juanmcasillas/BLButtons/doc/1_esquema.png

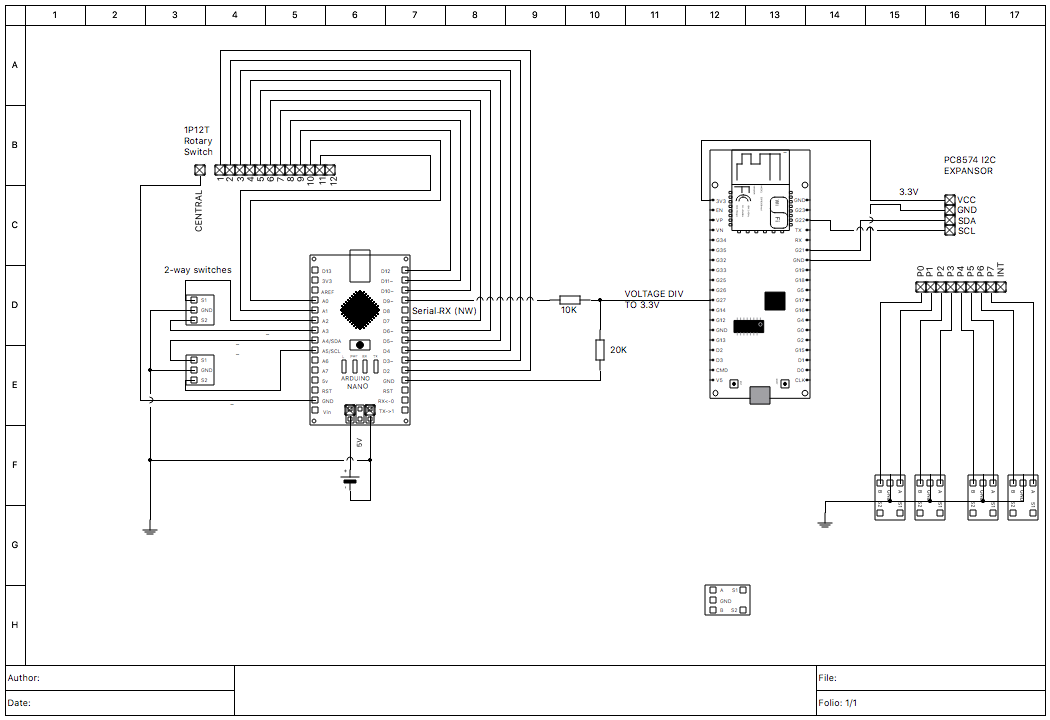
doc/1_esquema.png
