juanmcasillas/BLButtons/img/1p12t.jpg

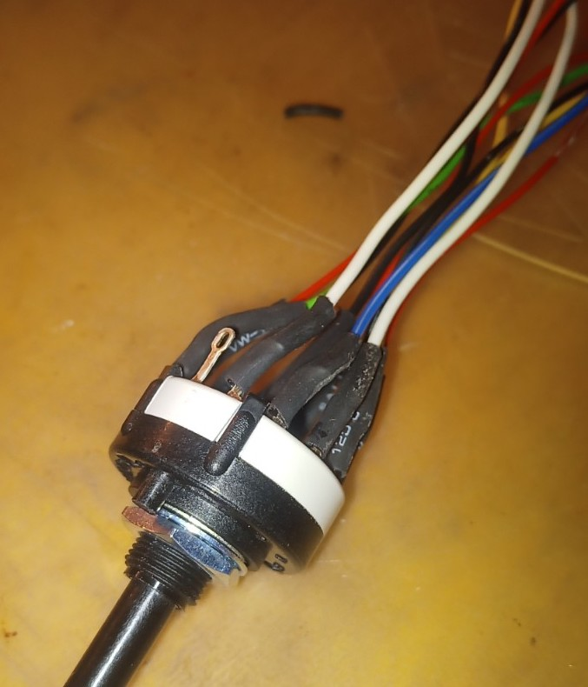
img/1p12t.jpg
