juanmcasillas/BLButtons/img/arduino_serial_esp32.jpg

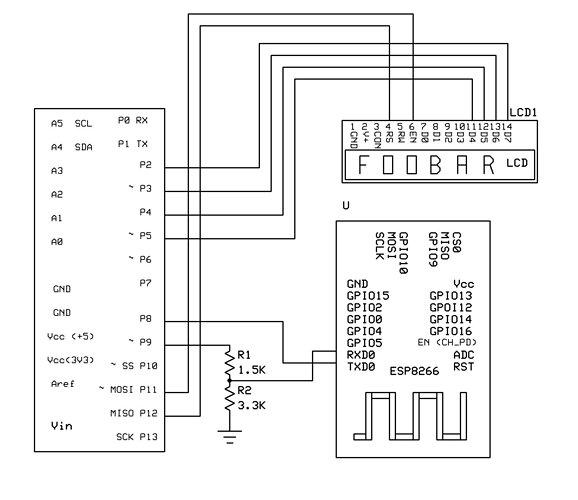
img/arduino_serial_esp32.jpg
