juanmcasillas/BLButtons/img/blbuttons.jpg

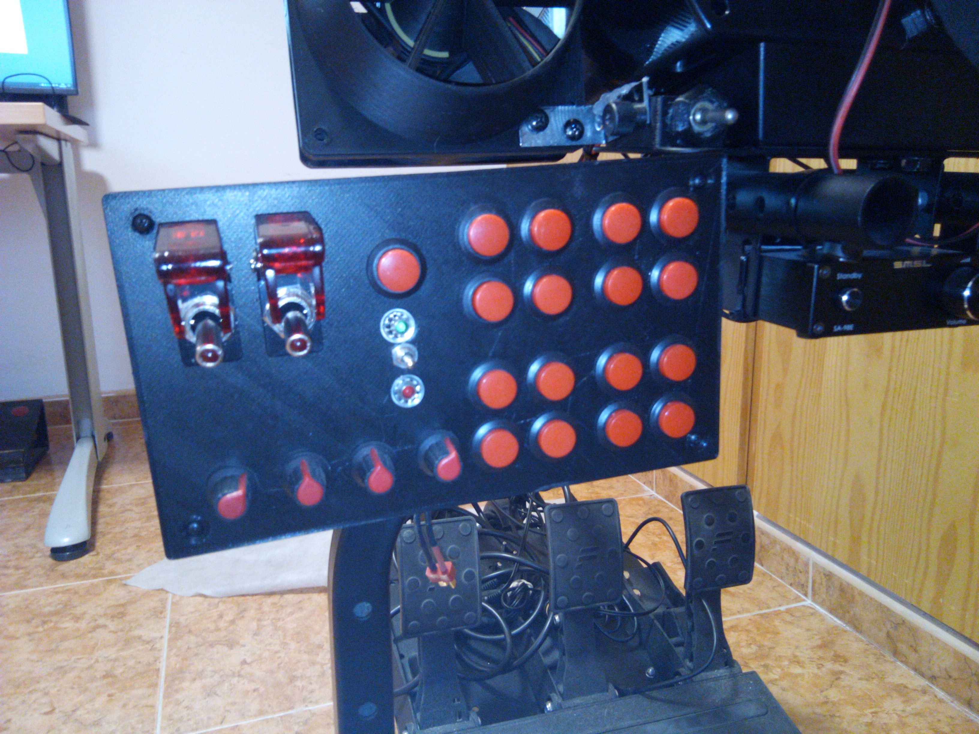
img/blbuttons.jpg
