juanmcasillas/BLButtons/img/box.jpg

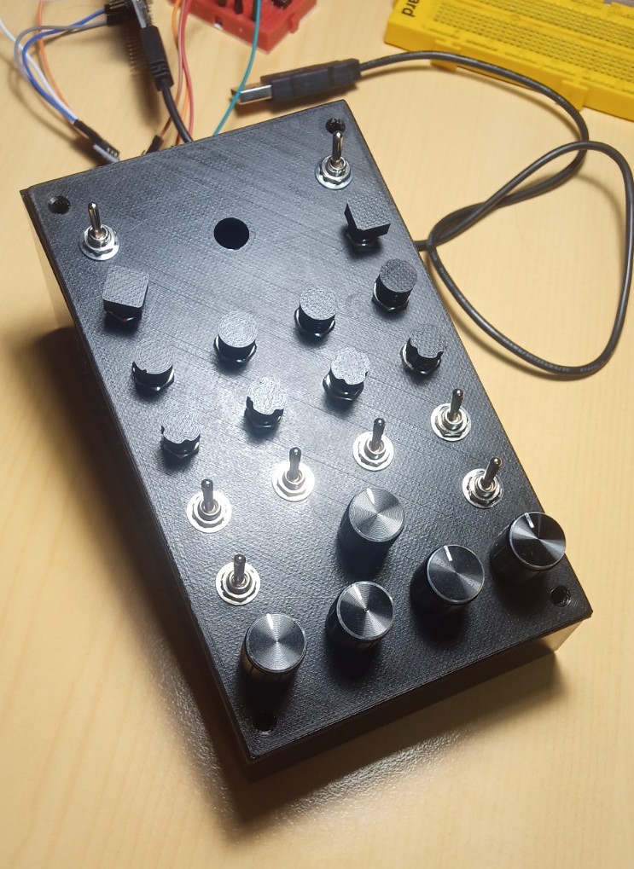
img/box.jpg
