juanmcasillas/BLButtons/img/esp32_photo.jpg

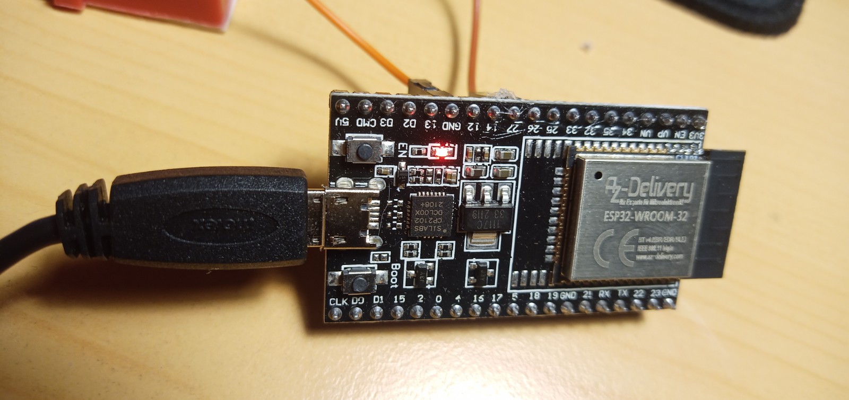
img/esp32_photo.jpg
