juanmcasillas/BLButtons/img/i2cexpansor.jpg

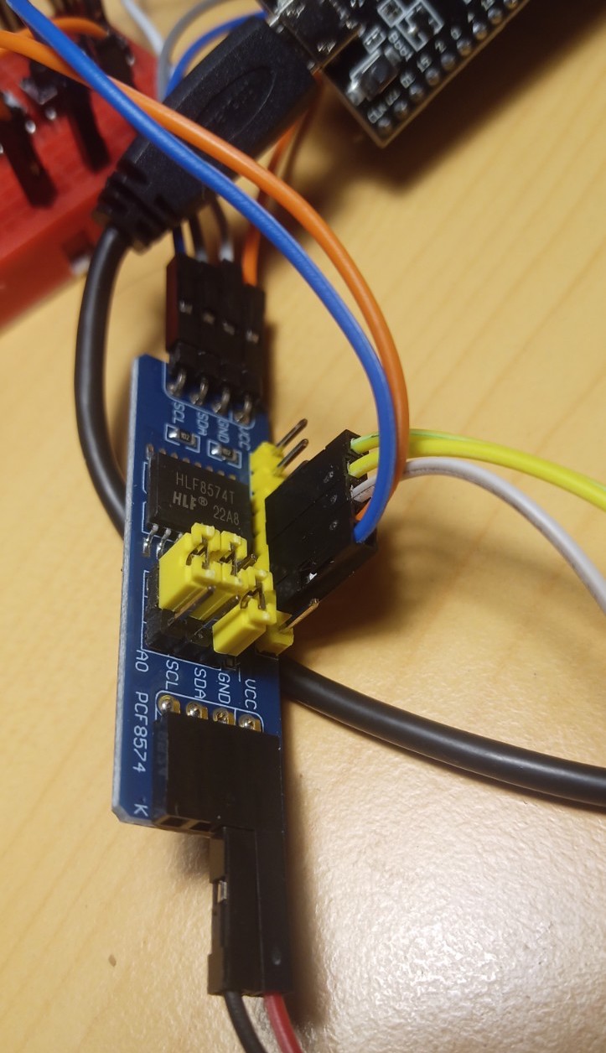
img/i2cexpansor.jpg
