juanmcasillas/BLButtons/img/keypad_matrix.png

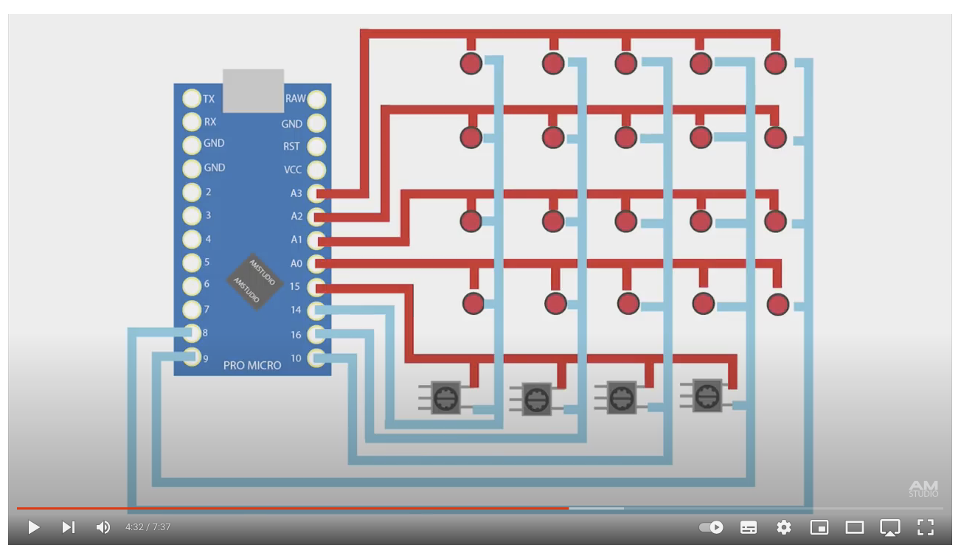
img/keypad_matrix.png
