juanmcasillas/BLButtons/img/keypad_matrix_encoder.png

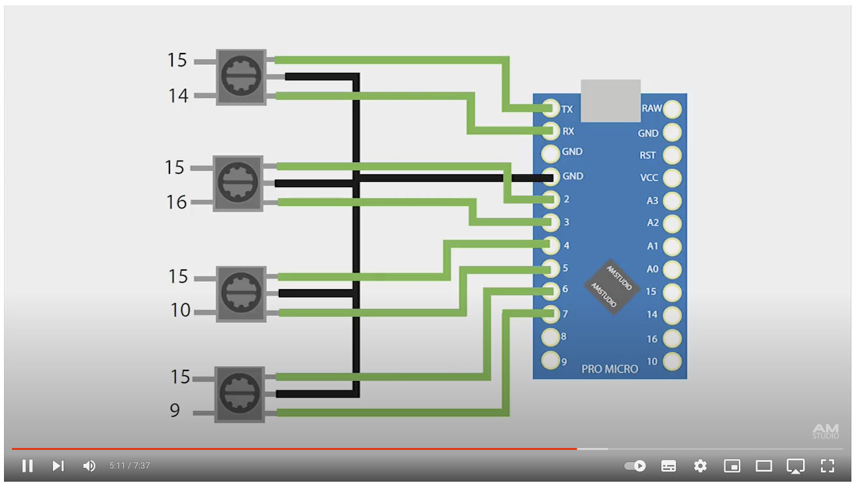
img/keypad_matrix_encoder.png
