juanmcasillas/BLButtons/img/keypadmatrix.png

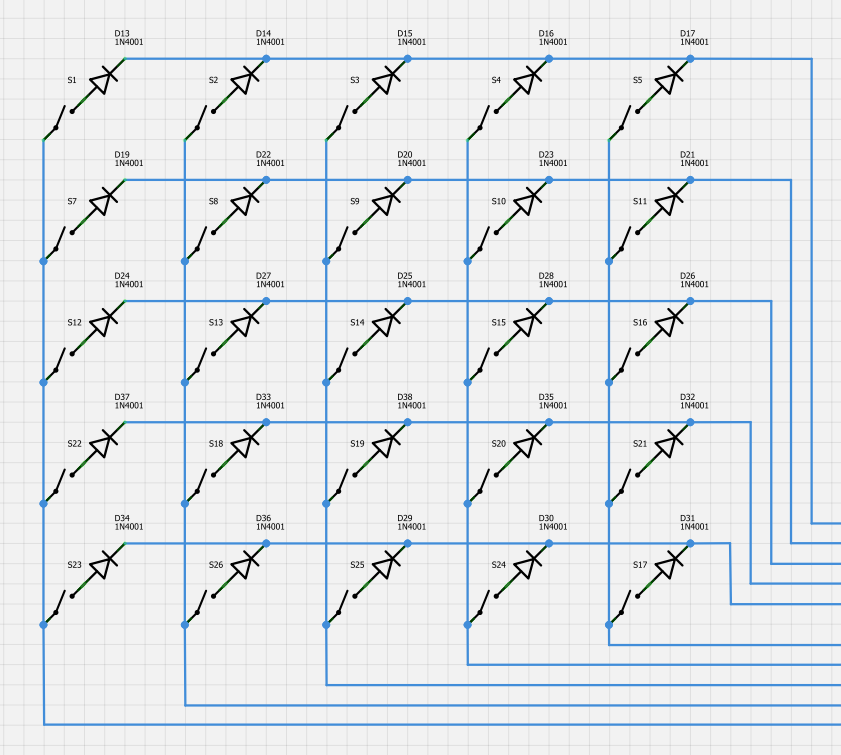
img/keypadmatrix.png
