juanmcasillas/BLButtons/img/ky_40.png

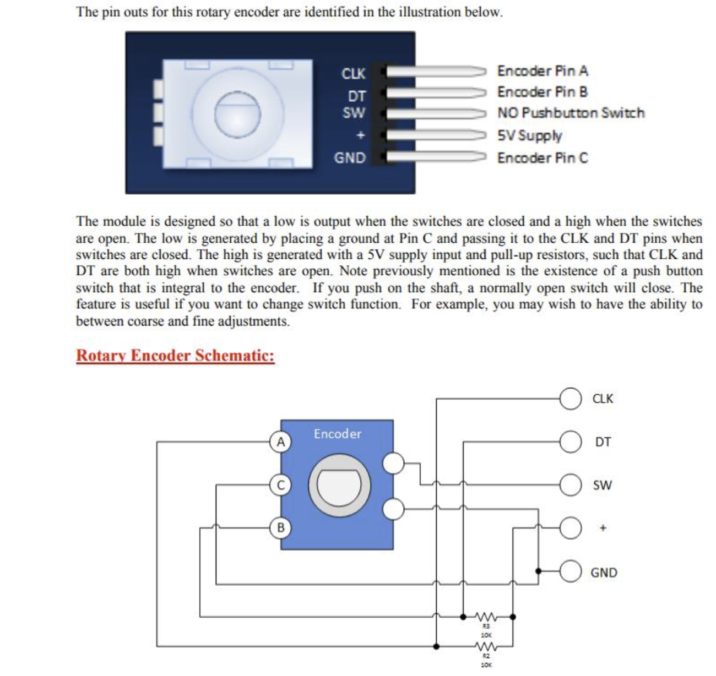
img/ky_40.png
