juanmcasillas/BLButtons/img/lever_cover_size.jpg

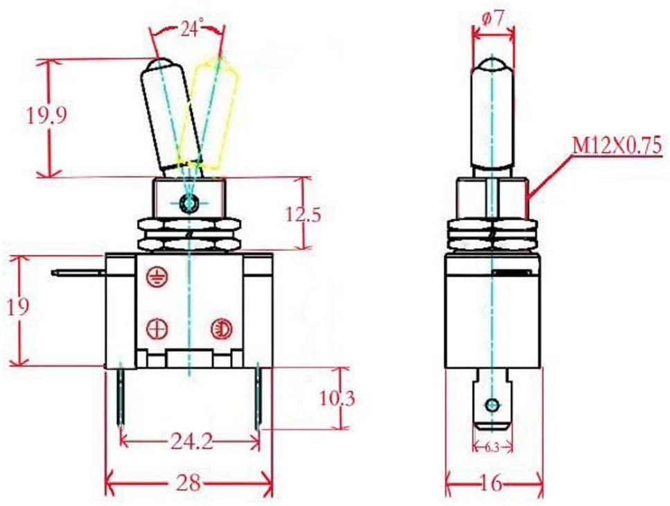
img/lever_cover_size.jpg
