juanmcasillas/BLButtons/img/lever_size.jpg

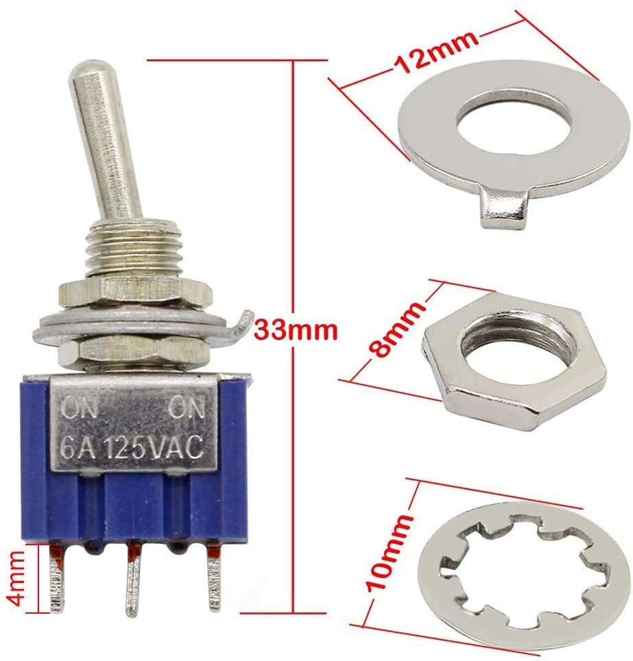
img/lever_size.jpg
