juanmcasillas/BLButtons/img/lever_size_cover.jpg

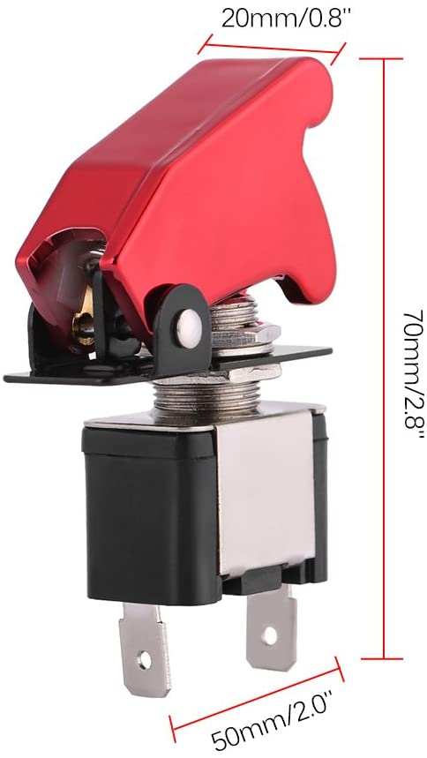
img/lever_size_cover.jpg
