juanmcasillas/BLButtons/img/PC8574module.jpg

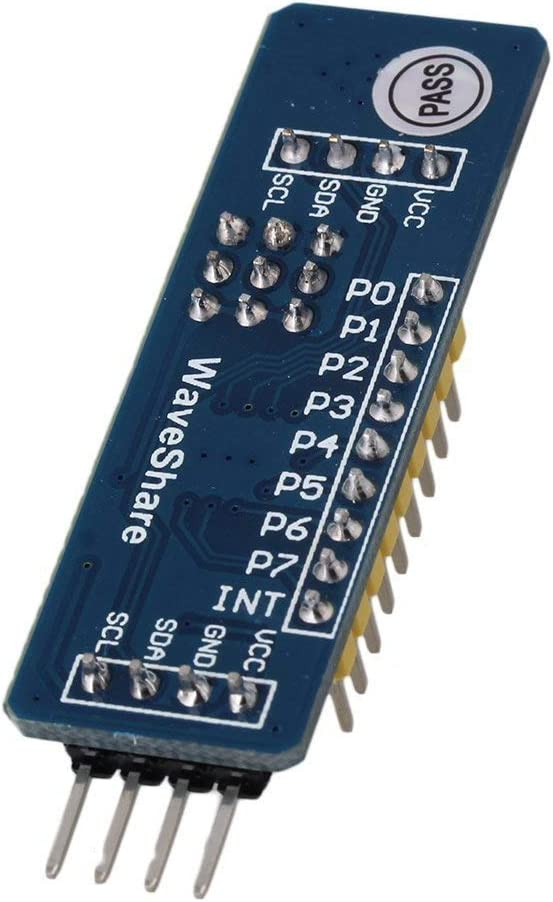
img/PC8574module.jpg
