juanmcasillas/BLButtons/img/pot_size.jpg

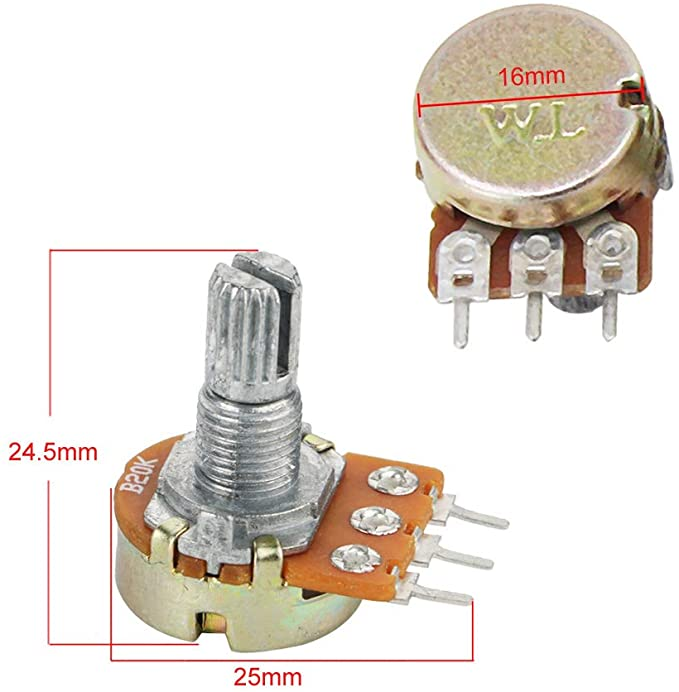
img/pot_size.jpg
