juanmcasillas/BLButtons/img/push_buttons.jpg

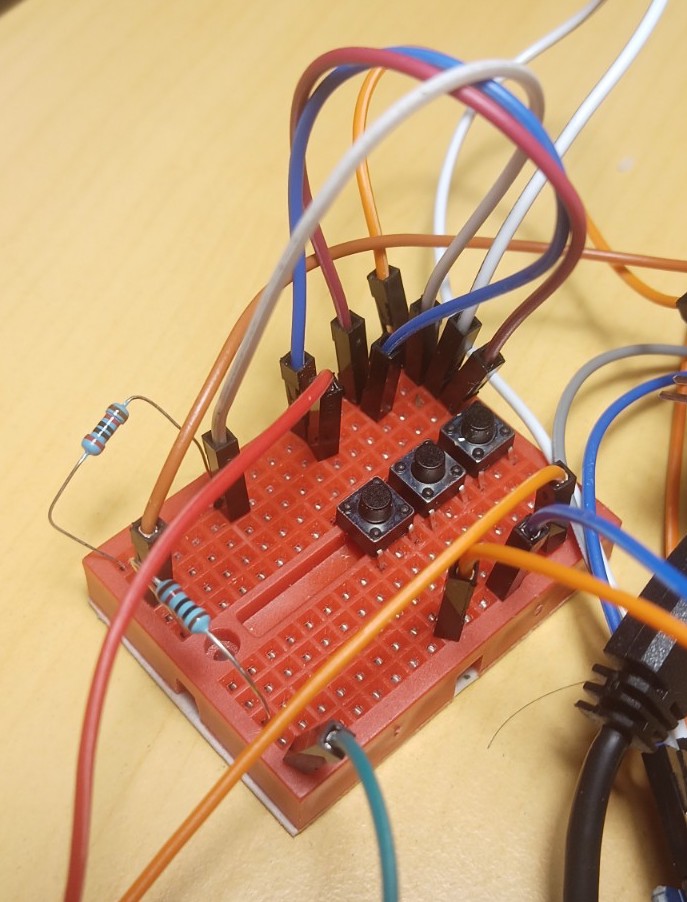
img/push_buttons.jpg
