juanmcasillas/BLButtons/img/push_size.jpg

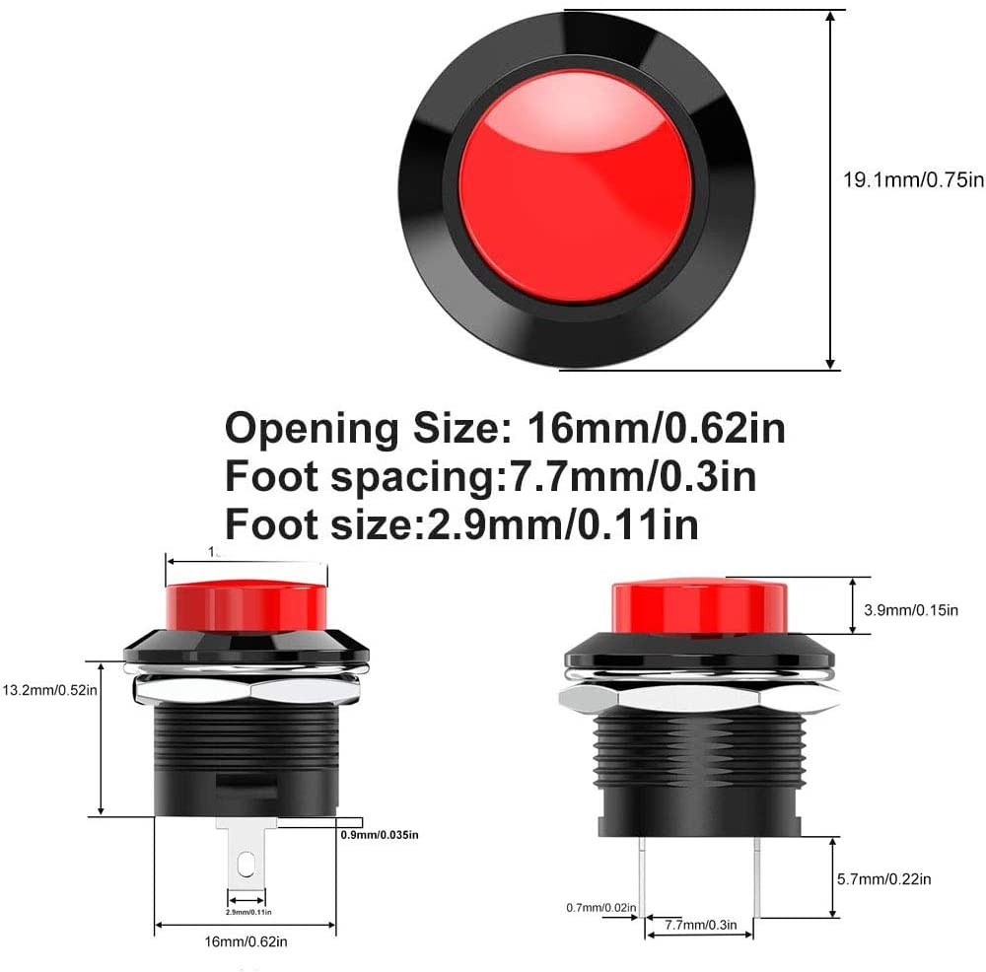
img/push_size.jpg
