juanmcasillas/BLButtons/img/radio/IMG-20230117-WA0001.jpg

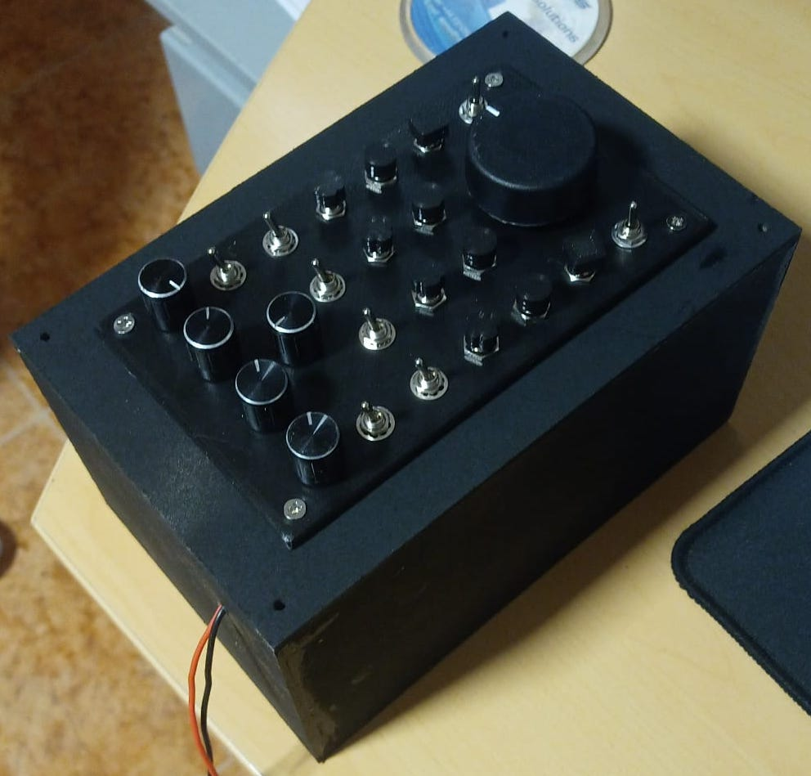
img/radio/IMG-20230117-WA0001.jpg
