juanmcasillas/BLButtons/img/radio/IMG_20221224_154635_948.jpg

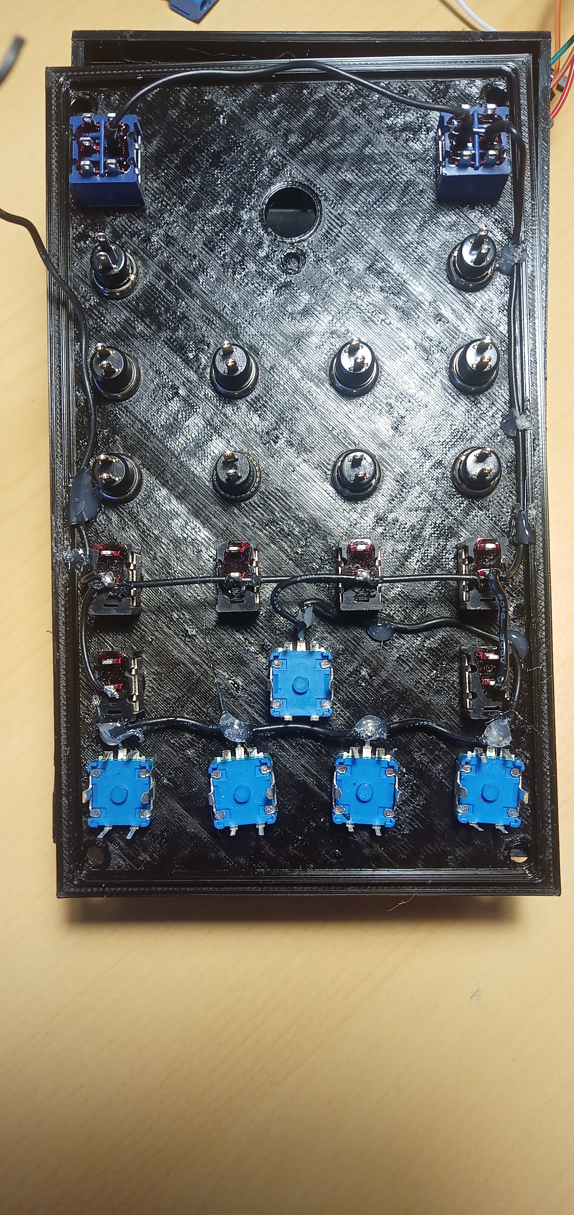
img/radio/IMG_20221224_154635_948.jpg
