juanmcasillas/BLButtons/img/radio/IMG_20230117_101055_758.jpg

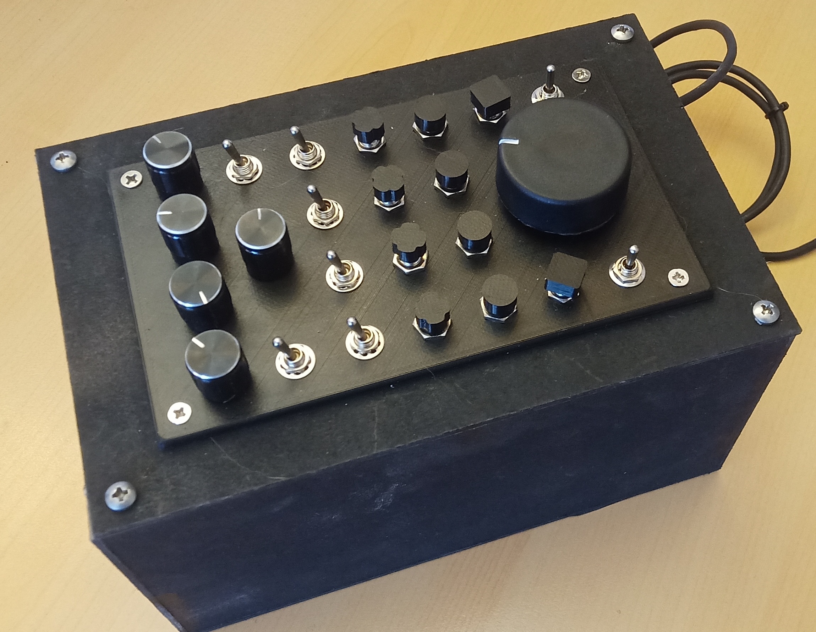
img/radio/IMG_20230117_101055_758.jpg
