juanmcasillas/BLButtons/img/radio/IMG_20230117_101122_997.jpg

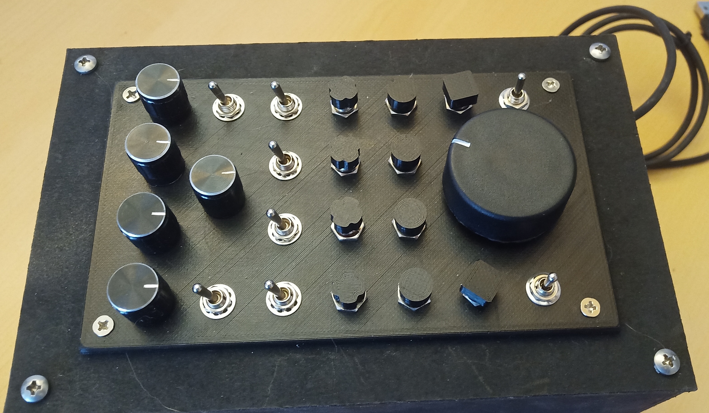
img/radio/IMG_20230117_101122_997.jpg
