juanmcasillas/BLButtons/img/tactile_switch.jpg

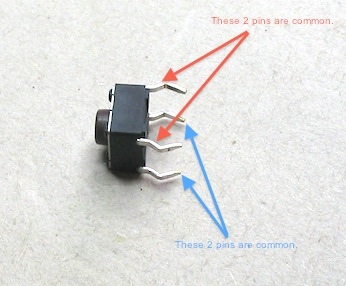
img/tactile_switch.jpg
