juanmcasillas/BLButtons/img/voltage_divider.jpg

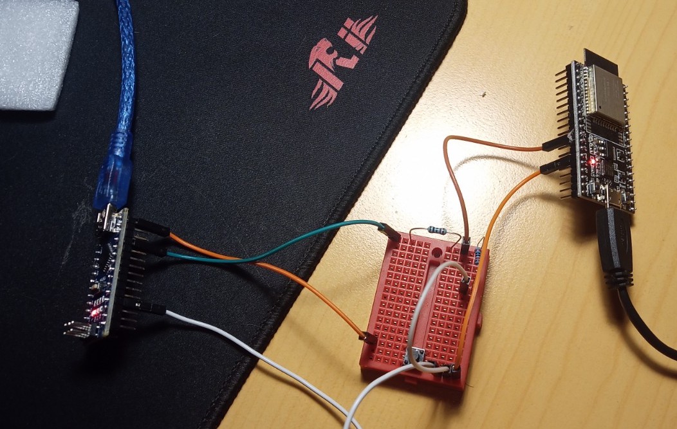
img/voltage_divider.jpg
