juanmcasillas/BLButtons/img/voltage_divider_big.jpg

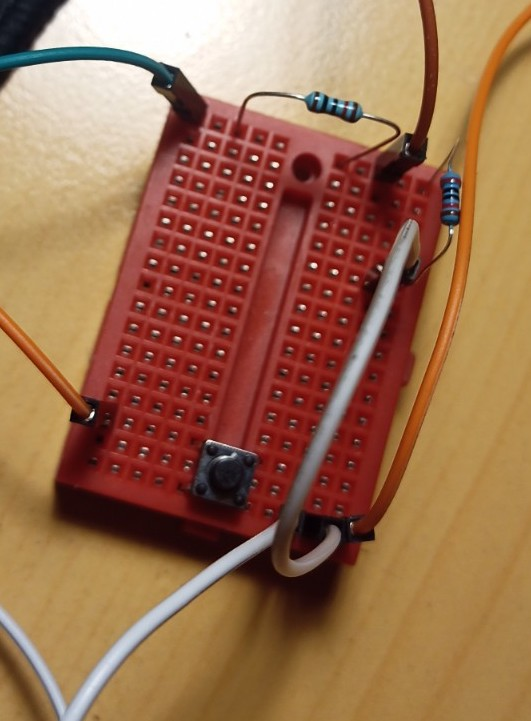
img/voltage_divider_big.jpg
