juanmcasillas/BLButtons/img/building/back.jpg

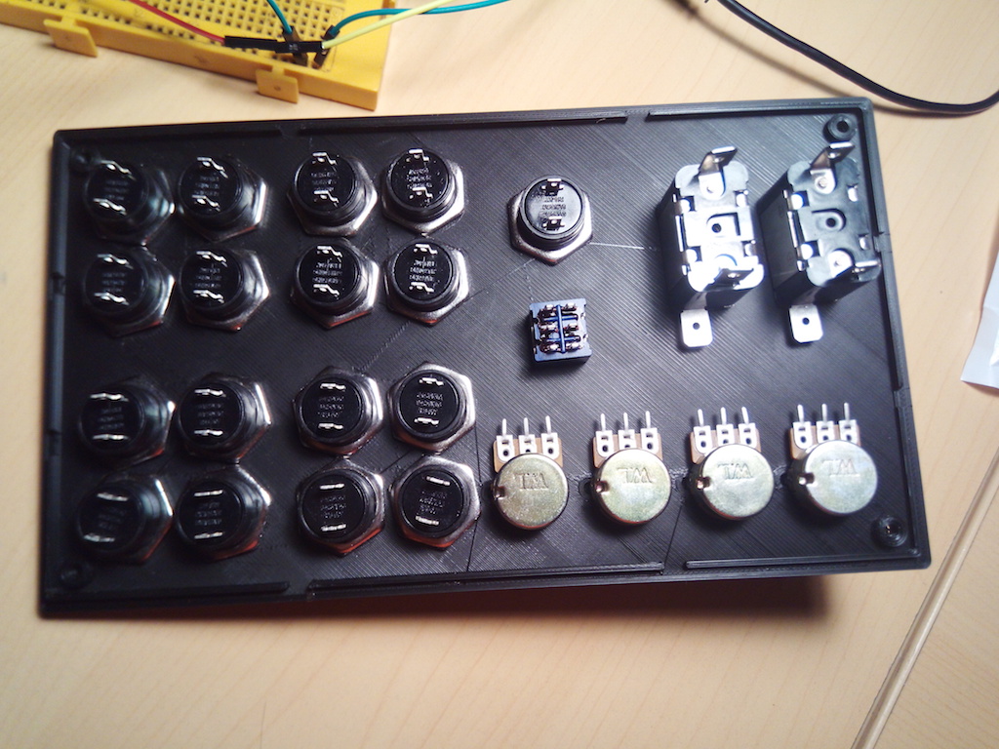
img/building/back.jpg
