juanmcasillas/BLButtons/img/building/cover.jpg

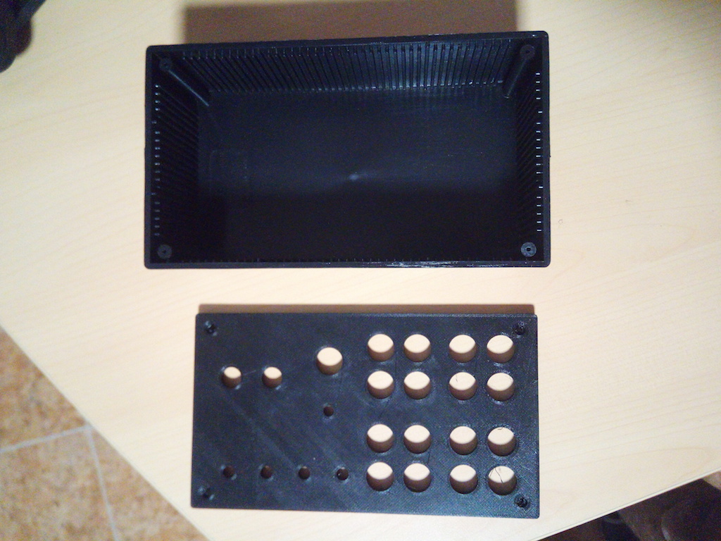
img/building/cover.jpg
