juanmcasillas/BLButtons/img/building/install_01.jpg

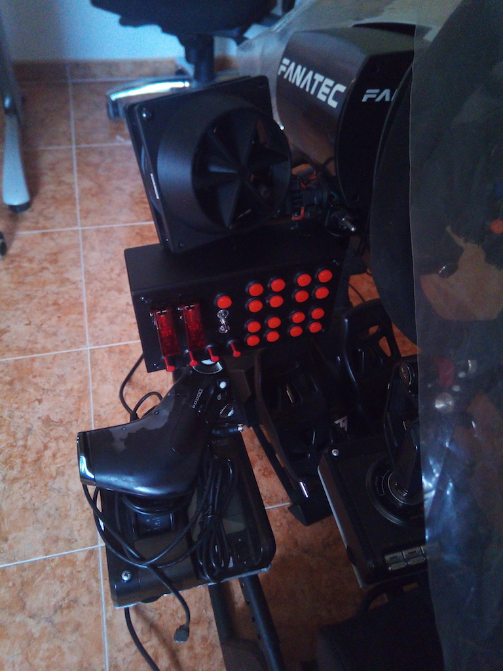
img/building/install_01.jpg
