juanmcasillas/BLButtons/img/GND_wiring.jpg

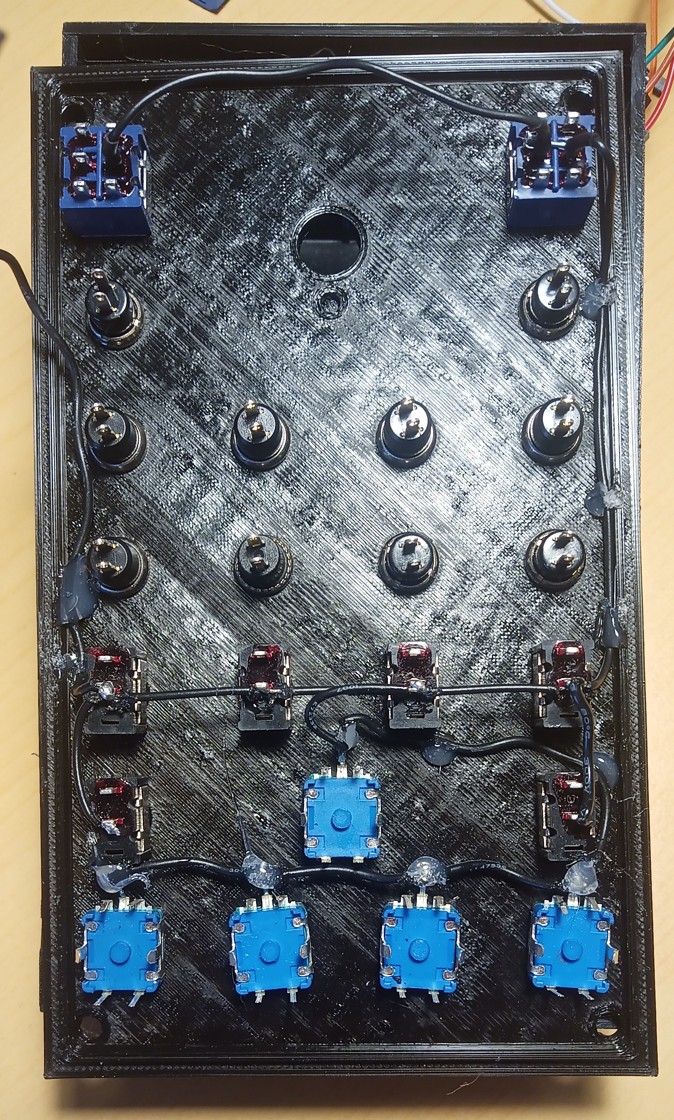
img/GND_wiring.jpg
