juanmcasillas/BLButtons/img/rotary_wiring_2.jpg

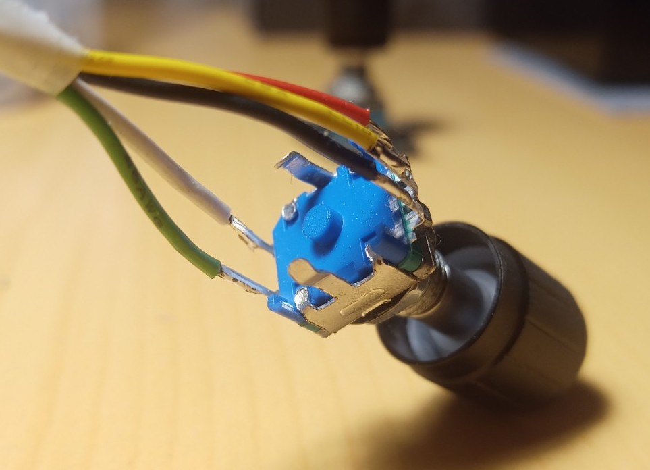
img/rotary_wiring_2.jpg
