juanmcasillas/BLButtons/img/usb_solder.jpg

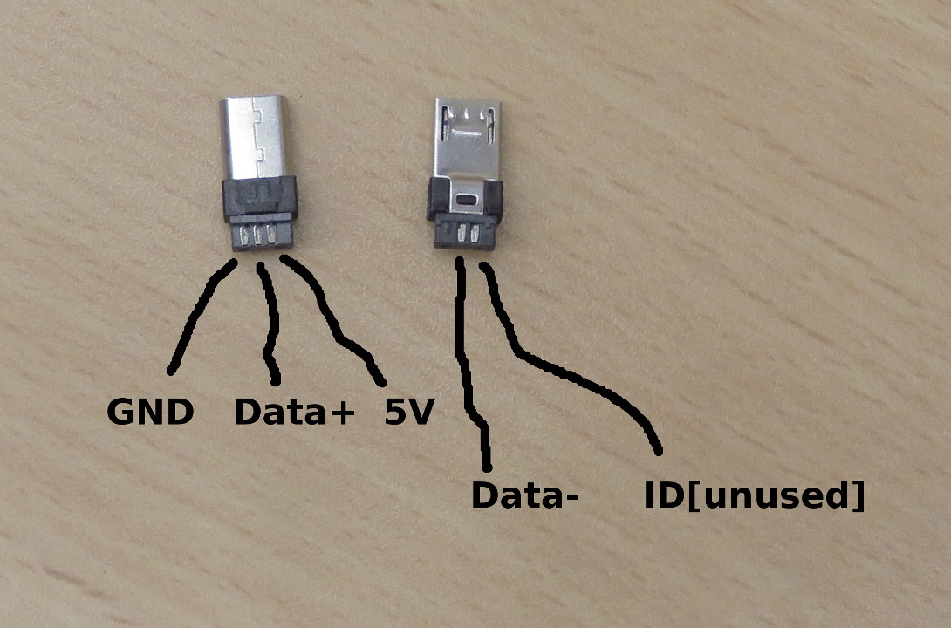
img/usb_solder.jpg
